luckylara/TissueVisionMods/CAD/MF_SM2_dichroic_holder/SM2_filter_holder.png

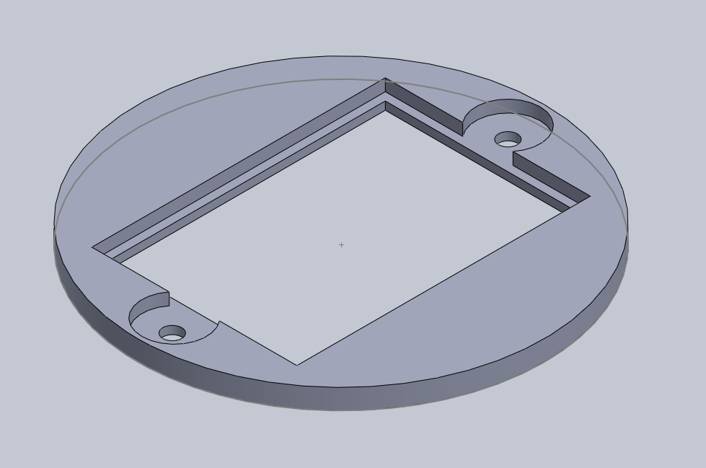
CAD/MF_SM2_dichroic_holder/SM2_filter_holder.png
