luckylara/TissueVisionMods/CAD/MF_SM2_dichroic_holder/SM2_filter_holder_picture_with_screw.jpg

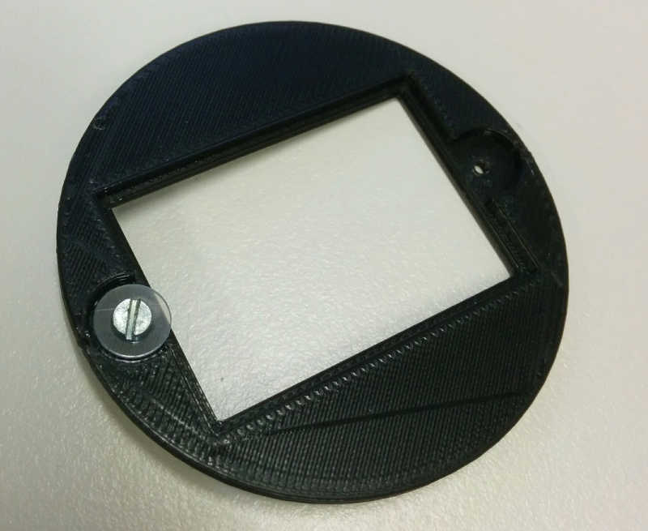
CAD/MF_SM2_dichroic_holder/SM2_filter_holder_picture_with_screw.jpg
