luckylara/TissueVisionMods/images/embeddingAndMounting/MF_embedding_mold_and_supports.jpg

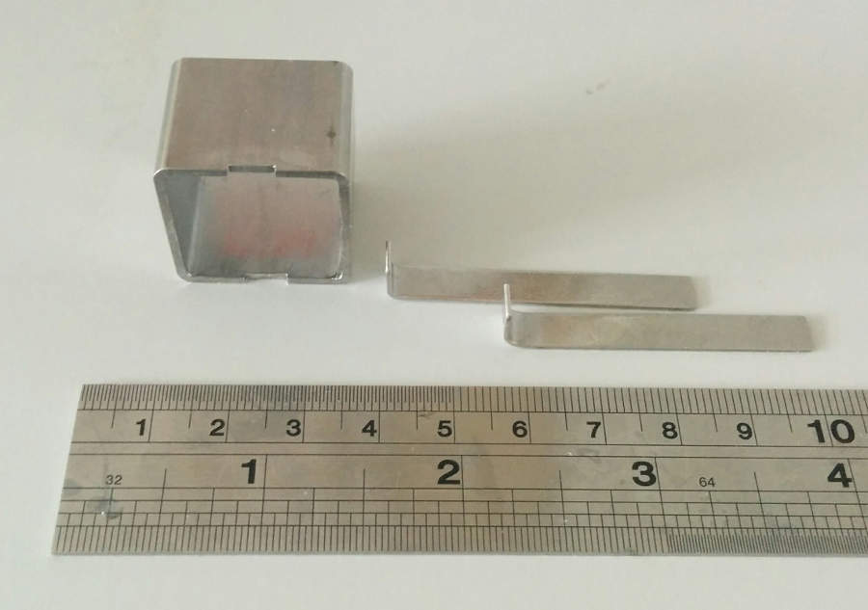
images/embeddingAndMounting/MF_embedding_mold_and_supports.jpg
