luckylara/TissueVisionMods/images/embeddingAndMounting/MF_slide_with_magnet_rear.jpg

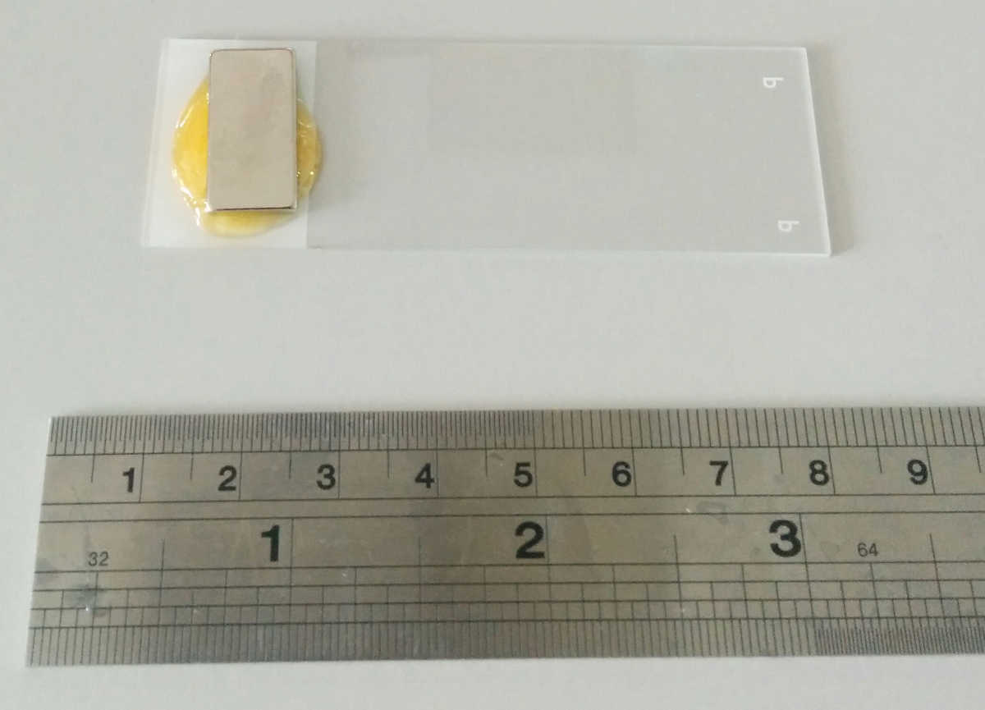
images/embeddingAndMounting/MF_slide_with_magnet_rear.jpg
