luckylara/TissueVisionMods/images/xy_stage/MF_stage_with_adjustable_pillars_02.jpg

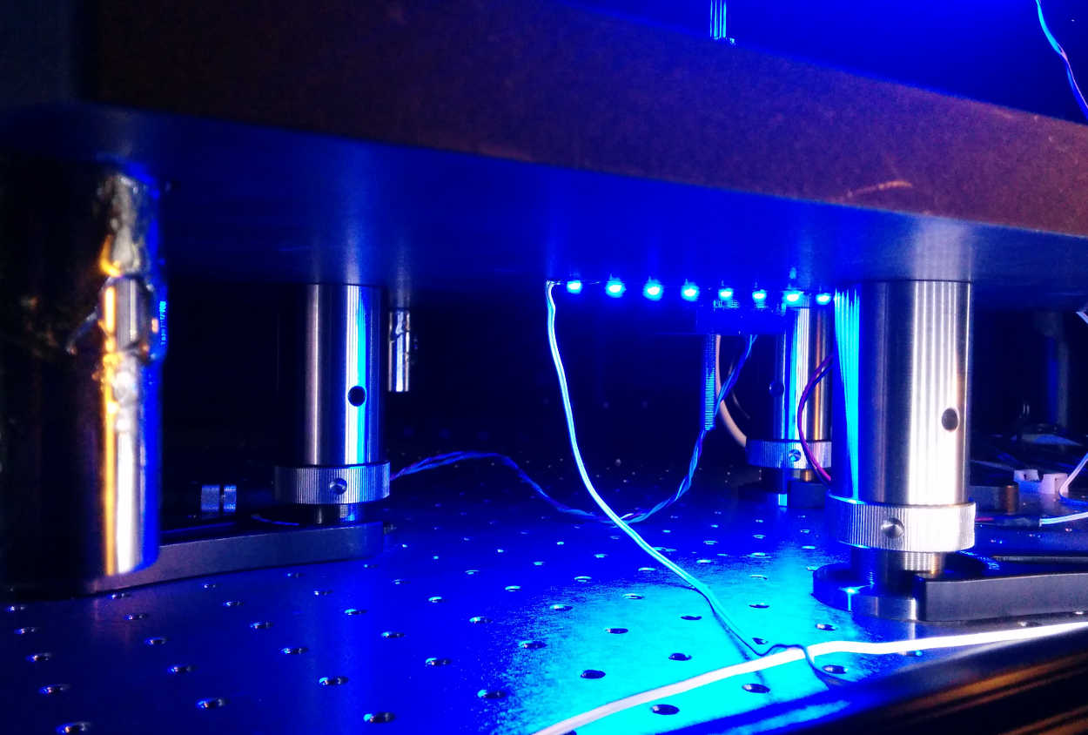
images/xy_stage/MF_stage_with_adjustable_pillars_02.jpg
